OpticalTechnologies/Autobalanced-Detector/Simulation/phase_shifter.asc

C2: cap; 100n
C3: cap; 100n
C4: cap; 100n
C5: cap; 4.7p
C9: cap; 10n
C10: cap; 10n
C11: cap; 100n
C12: cap; 4.7p
C13: cap; 10n
C14: cap; 10n
C15: cap; 100n
C16: cap; 4.7p
D1: diode; D0193
D2: diode; D0193
D4: diode; D0193
D5: diode; D0193
D6: diode; D0193
L1: FerriteBead; 10µ
L2: FerriteBead; 10µ
L5: FerriteBead; 10µ
L6: FerriteBead; 10µ
L7: FerriteBead; 10µ
L8: FerriteBead; 10µ
R3: res; 270
R5: res; 100
R6: res; 100
R7: res; 100k
R8: res; 10k
R12: res; 270
R13: res; 10k
R14: res; 100
R15: res; 100
R16: res; 50
R17: res; 10k
R18: res; 10k
R19: res; 270
R20: res; 100
R21: res; 100
R22: res; 100k
R23: res; 10k
R24: res; 10k
U2: LTC6228
U3: LTC6228
U4: LTC6228
V1: voltage; SINE(0 100mV 20e6 0 0 0); AC 1mV
V2: voltage; 2.5
V3: voltage; {bias}
V5: voltage; 2.5
V7: voltage; SINE(0 100mV 20e6 0 0 0); AC 1mV
V8: voltage; 15
V9: voltage; SINE(0 100mV 20e6 0 0 0); AC 1mV
V10: voltage; 0
Named nets: 0, +2.5, -2.5, PS1, PS2
;param bias = 0
.step param bias 0 15 1
.MODEL D0193 D( IS=6.0860E-15, N=1.0393, RS=.67651,IKF=.83333,CJO=94.082e-12,M=1.9777
+ VJ=6.1096,BV=35,IBV=5.0000E-6,TT=85.0000E-9
.ac dec 1000 100k 1G
;tran 0 1µs 0
;noise V(PS1) V7 dec 1000 100k 1G
