OpticalTechnologies/Autobalanced-Detector/Simulation/SRSDetV5.asc

C1: cap; 30p
C2: cap; 1n
C3: cap; 100n
C4: cap; {C_pd_par}
C5: cap; {C_lp}
C6: cap; 100n
C7: cap; 2.2µ; V=100 Irms=5.73 Rser=0.0196416 Lser=0 mfg="KEMET" pn="C1210C225K1RAC" type="X7R"
C8: cap; {C_lp}
C9: cap; 7p
C10: cap; 100n
C11: cap; 0.1µ; V=100 Irms=1.4 Rser=0.0913262 Lser=0 mfg="KEMET" pn="C0805C104K1RAC" type="X7R"
C12: cap; 0.1µ; V=100 Irms=1.4 Rser=0.0913262 Lser=0 mfg="KEMET" pn="C0805C104K1RAC" type="X7R"
C13: cap; 0.1µ; V=100 Irms=1.4 Rser=0.0913262 Lser=0 mfg="KEMET" pn="C0805C104K1RAC" type="X7R"
C14: cap; 0.1µ; V=100 Irms=1.4 Rser=0.0913262 Lser=0 mfg="KEMET" pn="C0805C104K1RAC" type="X7R"
C15: cap; 1µ; V=100 Irms=1.4 Rser=0.0913262 Lser=0
C16: cap; 100n
C17: cap; 0.1µ; V=100 Irms=1.4 Rser=0.0913262 Lser=0 mfg="KEMET" pn="C0805C104K1RAC" type="X7R"
C18: cap; 0.1µ; V=100 Irms=1.4 Rser=0.0913262 Lser=0 mfg="KEMET" pn="C0805C104K1RAC" type="X7R"
C19: cap; 0.1µ; V=100 Irms=1.4 Rser=0.0913262 Lser=0 mfg="KEMET" pn="C0805C104K1RAC" type="X7R"
C20: cap; 0.1µ; V=100 Irms=1.4 Rser=0.0913262 Lser=0 mfg="KEMET" pn="C0805C104K1RAC" type="X7R"
C21: cap; 82p
C22: cap; {Cfb}
C23: cap; 5p
D1: diode
D2: zener; 1N750
D3: zener; BZX84C10L
I1: current; PULSE(0mA 2mA 0 0.1n 0.1n 12.5ns 25ns)
I5: current; SINE(0 1e-5 20e6 0 0 90)
I6: current; ""; AC {I_ac} 0
L1: ind2; 470n; Rser={R_ser} Cpar=10p
L2: ind2; {L_lp}; Rser={R_ser} Cpar={C_paras}
L3: ind2; {L_lp}; Rser={R_ser} Cpar={C_paras}
L4: FerriteBead; 1µ
L5: FerriteBead; 1µ
L6: ind; 180nH; Rser=0.64 Cpar=1.16p
Noise_Input: current; {Ip}; AC 0 0
Q1: npn; BC847C
Q2: npn; BC847C
R1: res; 10k
R2: res; 10k
R3: res; 50
R5: res; 10
R6: res; 10k
R7: res; 1
R8: res; 10k
R9: res; 10
R11: res; 50
R12: res; 1k
R13: res; {D_ser}
R17: res; 1k
R18: res; 1k
R19: res; 51
R20: res; 51
R_Shotnoise1: res; 6.035e-5
ShotNoise1: g; {I_shot*1e12}
TransmittionModulation: current; PULSE(0mA 0.2mA 0 5n 5n 2µ 4µ)
U1: AD8031
U3: OPA847
V1: voltage; 3V; Rser=0
V2: voltage; -3V; Rser=0
V3: voltage; 5; Rser=0
V4: voltage; 22V; AC 0; Rser=0
V5: voltage; 10V; Rser=0
Named nets: 10V, 0, 3.3V, -3.3V, 5V, SIG_RFSA_Signal, Vrb
;tran 0 10µs 1µs
.ac dec 1000 10k 1G
;noise V(SIG_RFSA_SIGNAL) Noise_Input dec 500 1e4 1e9
Photodiode mit Shotnoise - Erweitertes Modell
.param Ip=1mA
.param I_shot = sqrt(2 * 1.602e-19 * Ip)
.param I_ac = 1mA
;step param Ip list 0mA 0.5mA 1mA 1.5mA 2mA 3mA 4mA 5mA 6mA 8mA 10mA
Noise in dBm/Hz:
10*log10((V(onoise)*sqrt(1Hz)/1V)**2/50*1000)
 
TIA-Gain in dBt (ref: gain over 1Ohm: 1V/A): 
sqrt(V(SIG_RFSA_Signal)/1nV)
.param Cfb = 0.5p
;step dec param Cfb 0p 1p 5
.param C_lp 100p
.param L_lp 470n
.param C_paras = 1.16p
.param C_paral = 10p
.param R_ser = 0.62
;step dec param C_lp 10p 100p 5
.param C_pd_par 60p
.param D_ser 0.1
;step dec param D_ser  10 1000 3
